fschoning/Hermes-Lite2/hardware/companions/gowin-bridge/ROUTING.md

# gowin-bridge routing guide, rev D

**Routing by hand in EasyEDA Pro and ordering from JLCPCB: see
`ROUTING_EASYEDA.md` instead — that is the procedural, step-by-step guide.
This file is the KiCad-era background it was built from.**

For whoever lays this board out. The schematic is generated and
validated. **Since 13 Sep 2026 the board is not placed either**: only the
parts the radio, the dock and the case fix are on it, and it goes to Quilter
for placement and routing (`QUILTER.md`). The rules below are what the
returned board is checked against.

**One design, one board, one connector.** rev C's three-socket fan-outs,
upright-fin transitions and panel V-scores do not exist any more.

| | |
|---|---|
| Board | radio end **64.50 × 64.88 mm** (outline from local y 0.07), local (0,0) = HL2 main board (70.00, 73.30); whole board with the Gowin end 64.50 × 92.00 mm, no rails, ends joined by three mouse-bite tabs |
| Stack | **4 layer**, 1.6 mm. F.Cu signal / **In1.Cu solid GND** / In2.Cu power / B.Cu signal |
| Unrouted nets at handover | 328 items, DRC otherwise **0 violations** |
| Impedance | target **100 Ω differential**, **not** guaranteed — JLCPCB Economic gives no impedance control and `COST.md` §5.1 explains why buying it would waste $33.88 |

---

## 1. The four rules that are not negotiable

1. **In1.Cu is a solid ground plane and nothing crosses it.** Every
   differential pair references it. Do not route on In1.Cu, do not cut it, and
   do not let a via field starve it under the connector.
2. **Every single-ended net that touches an HL2 header pin stays under
   25 mm.** That is what the floor plan is built for: the translators and LVDS
   silicon sit in local x 9…53, y 12…34, right beside DB1 and DB12. The long
   runs are the terminated differential pairs up to the connector, and they do
   not care.
3. **Each received pair's 100 Ω termination goes within 5 mm of the receiver
   pins.** Eight of them. There is no termination at a driver output and none
   should be added.
4. **Each ESD array goes within 5 mm of the SlimSAS contacts**, on the
   connector side of the terminations, the series resistors and the buffers,
   with the shortest possible ground return. Twelve of them. An ESD clamp
   behind the thing it protects protects nothing.

## 2. The order to route in

| | What | Why first |
|---|---|---|
| 1 | **The four forward-group pairs** — `A_FWDCLK`, `A_ADCD0`, `A_ADCD1`, `A_ADCD2`, on connector positions 14/15, 17/18, 20/21, 23/24 | They are the only pairs whose **skew has to match each other**. Length-match them to within about 2.5 mm (which is 15 ps, under 0.5 % of a 3.2552 ns unit interval). They are four contiguous pairs each flanked by grounds, so they fan out cleanly |
| 2 | **The four reverse-group pairs** — `B_REVCLK`, `B_TXD0`, `B_TXD1`, `B_TXD2`, on the same position numbers in row B | Same rule, same tolerance |
| 3 | **The auxiliary pairs** — `A_AUXCLK`, `A_AUXDAT` on 2/3 and 5/6, and their row B counterparts | Clock and data must match each other; they need not match the forward group |
| 4 | **The duplicate clock pair** on 32/33, and the spare on 35/36 | No matching requirement at all |
| 5 | **The 12 ESD arrays**, then the 8 terminations | Rules 3 and 4 above. Do these before the single-ended routing takes the space |
| 6 | **The single-ended HL2 nets** | Rule 2. `HL2_FWD_CLK_RAW` → R1 → `HL2_FWD_CLK` → U1 is the shortest one worth caring about: 132 Ω of Thevenin into ~4 pF is 0.53 ns, and a long stub would add to it |
| 7 | **The 16 sideband conductors** | Slow. TCK at 24 MHz is the fastest; the AUXIO lines are DC to 400 kHz |
| 8 | **The JTAG run from CN1 to the connector** — about 59 mm | Deliberately allowed to be long. 41.7 ns of TCK period against 0.085 ns of added electrical length |
| 9 | **Power** | See §4 |

## 3. Differential-pair geometry

* **Route both legs of a pair on the same layer, side by side, over In1.Cu.**
  Do not split a pair between F.Cu and B.Cu.
* **Ground on both sides where there is room.** The connector gives you a
  ground contact between every pair for free — positions 1, 4, 7, 13, 16, 19,
  22, 25, 31, 34 and 37 in both rows — so stitch them.
* **Via transitions in pairs, with a ground via beside each.** Keep them to a
  minimum; ideally the forward group never changes layer.
* **P is always the lower-numbered contact** in both rows. `check_netlist.py`
  asserts it, because getting it wrong on one pair inverts one lane.
* **Do not add anything to a pair** — no series resistors, no AC coupling, no
  test points. rev C offered AC coupling as an option; rev D does not, because
  every lane has a fixed direction and a series capacitor on a driven pair is
  just an impedance discontinuity.

## 4. Power

* **`DB1_3V3` → FB1 → `+3V3`.** Put the 10 µF on the DB1 side and the 10 µF on
  the `+3V3` side, so the bead sees a capacitor on both sides. Wide copper:
  the board takes 350 mA and the radio's own feed to DB1 pins 19/20 has no
  filtering of its own.
* **In2.Cu is the power layer.** `+3V3` pours over most of it; the `+2V5`
  island spans local x 8…33, y 1…12 and has to reach U1's and U2's VCCA, U3's
  VCCB, U12's output and the `SL_VLVDS` link.
* **One 100 nF per supply pin, on the same side as the pin, via straight to
  the plane.** There are 22 of them and they are not decoration: the
  translators switch 15 pF of internal Cpd per channel at 153.6 MHz.
* **U12, the 2.5 V LDO, dissipates 40 mW.** No thermal work needed.

## 5. The mechanical constraints the router must respect

| | |
|---|---|
| **The three sockets are on the BOTTOM** (J2 on DB1, J3 on DB12, J4 on CN1) and their hole positions are fixed by the radio. Do not move them by so much as 0.01 mm — `check_geometry.py` recomputes all 36 holes from `hermeslite.kicad_pcb` and fails if they move |
| **The connector is at local (10.40, 46.00)** and its position is load-bearing: `DESIGN_NOTES.md` §6.2 shows it cannot go anywhere else. Do not "tidy" it toward the middle of the front edge |
| **The M3 anchor is a U-notch** at local x 1.30…4.70, from y 61.95 to the top edge. Keep copper 0.3 mm clear of it |
| **The cut-outs**: a notch over the radio's FPGA (local x 24.00…50.20, top edge to y 25.10) and one cut-out over the AD9866, T2, jumper DB6 and header DB3 (local x 34.09…57.87, y 30.00…56.25, with a step at x 48.00 down to y 34.01). Nothing within 1 mm; pairs 2 mm off; **fast nets 3 mm off, and no track at all within 3 mm of DB3 pins 3 and 4**, the AD9866 input. `DESIGN_NOTES.md` §13, §14.4, §14.5 |
| **The noise rules at the radio end** — no track on the bottom layer (it is a solid ground pour facing the radio); fast nets 3 mm from every edge (`bridge/bridge.kicad_dru` checks it); the 48 pre-placed ground vias round the cut-outs stay. `DESIGN_NOTES.md` §14.4 |
| **J5, the JTAG pass-through, must stay reachable with the board fitted** — since 13 Sep 2026 it is horizontal on the top, pin 1 at local (51.40, 30.80), rotation 90, just below J4; a USB Blaster's 10-way IDC socket needs about 20 × 12 mm of clear space above it and 15 mm of height |
| **The 1.1 mm unplated hole at local (4.04, 2.12)** is the optional locating peg into HL2 MH6 |

## 6. Fault-finding, in the order to try it

| Symptom | First suspect |
|---|---|
| **Nothing at all, both directions** | Read test point `SB_PRSNT_IN`. `R_DRVEN_PRSNT` is fitted, so with a no-sideband cable, or a Gowin whose gateware does not drive presence, the drivers are disabled and the board looks dead |
| **Forward link trains, but nothing reaches the radio** | Read test point `LINK_ALIVE`: about 2.2 V with the forward clock running and a far end present. Near 0 V means the receivers, JTAG and AUXIO buffers are all tri-stated: check the clock at `HL2_FWD_CLK` and presence at `SB_PRSNT_IN` |
| **The forward link does not train** | Scope R1's DB1-side pad (the raw clock), then test point `HL2_FWD_CLK` (after the divider — expect 2.50 V high), then U1 pin 13 (the translator output into the driver). If the divider level is low, pin 98 is not set to 8 mA drive |
| **Forward clock fine, data garbled** | Skew. The forward group must be length-matched. Check that all four went through U1 and U4 and that nothing was split across packages |
| **The forward link works but every bit is inverted** | The connector's A1 end is at the other physical end than the footprint assumes. Harmless and recoverable — invert the lane in gateware. `PINMAP.md` §1.1 |
| **The reverse clock is absent** | `R_CLKSEL_A` must be fitted and `R_CLKSEL_B` must not. If the primary clock lane is physically damaged, swap them |
| **The reverse data has a marginal eye** | This is the tightest path on the board: DB1 pins 11/15/17 are the LED pins, and a 3.3 V output into 15 pF gives a 1.65 ns rise against a 3.2552 ns unit interval. The series parts are 0 Ω on 0402 pads; do not raise them past 22 Ω |
| **The auxiliary link works one way only** | Clock and data must be in the same translator port. Probe the two 0 Ω links into DB12 pins 5 and 2 |
| **The radio's auxiliary clock input sees the reverse clock too** | HL2 **R17** is fitted. It must not be — it shorts the DB12 pin 5 and pin 6 nets through 100 Ω |
| **JTAG over the cable does nothing** | Read test point `JTAG_EN_N`: HIGH means disabled, which is the power-up state and the correct state until the gateware asserts it. If the gateware cannot run, fit `R_JTAG_FORCE` |
| **A locally plugged USB Blaster misbehaves** | Test point `JTAG_EN_N` should read HIGH while a Blaster is plugged in. If it reads LOW, the remote path is driving CN1 at the same time |
| **The radio's CW/PTT or I2C behaves oddly** | Read test point `AUXIO_OE_N`. HIGH is read-only and is the power-up state; it can only go LOW while `AUXIO_EN_N` is LOW **and** `LINK_ALIVE` is HIGH **and** a powered far end holds `SB_PRSNT_IN` high. If it is LOW, the far end is driving four of the radio's pins |
| **The radio browns out or resets when the board is fitted** | Was the board plugged in with the radio powered? That is a 22 A microsecond event. Otherwise measure the radio's 3.3 V rail: the board should draw about 350 mA |

## 7. The bring-up sequence, and the safety check comes first

0. **On the bench, before any radio:** power the board from 3.3 V on DB1 pins
   19/20, hold `SB_PRSNT_IN` HIGH through 1 kΩ, and put a 153.6 MHz square wave
   on DB1 pin 9. Test point `LINK_ALIVE` must read about 2.2 V; with the
   signal off, under 0.1 V.
1. **With stock gateware, then with no gateware, and no cable plugged in**,
   power the radio with the board fitted and read test points `LINK_ALIVE`,
   `JTAG_EN_N` and `AUXIO_OE_N`. **`LINK_ALIVE` must read near 0 V and the other
   two HIGH**, even though stock gateware drives `AUXIO_EN_N` LOW. That is the
   whole safety property and it is the first thing to confirm, before anything
   is driven.
2. Check test points `+3V3` and `+2V5`, and measure the radio's 3.3 V rail current
   with and without the board.
3. Read test point `SB_PRSNT_IN` with the cable out (expect 0 V) and in, with the far
   end powered (expect 3.0 V).
4. Scope the forward clock chain: R1's DB1-side pad, test point
   `HL2_FWD_CLK`, U1 pin 13.
5. Bring up the forward link, then the reverse link, then the auxiliary link.
6. Only then enable JTAG over the cable, and only with no USB Blaster plugged
   into J5.
7. Leave the AUXIO drive path disabled unless you specifically want it. It can
   reach the radio's master-clock generator.
8. Run the noise test plan in `DESIGN_NOTES.md` §14.6.
